encarbassot/keyboard/documentation/joystik.png

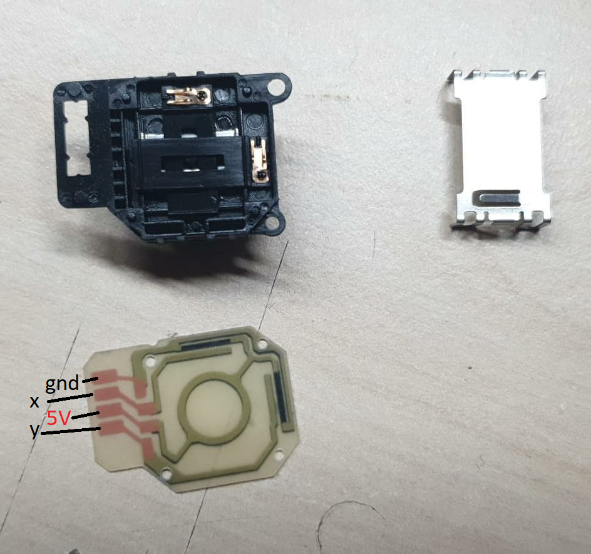
documentation/joystik.png
