encarbassot/keyboard/documentation/proMicro-deco-mux.png

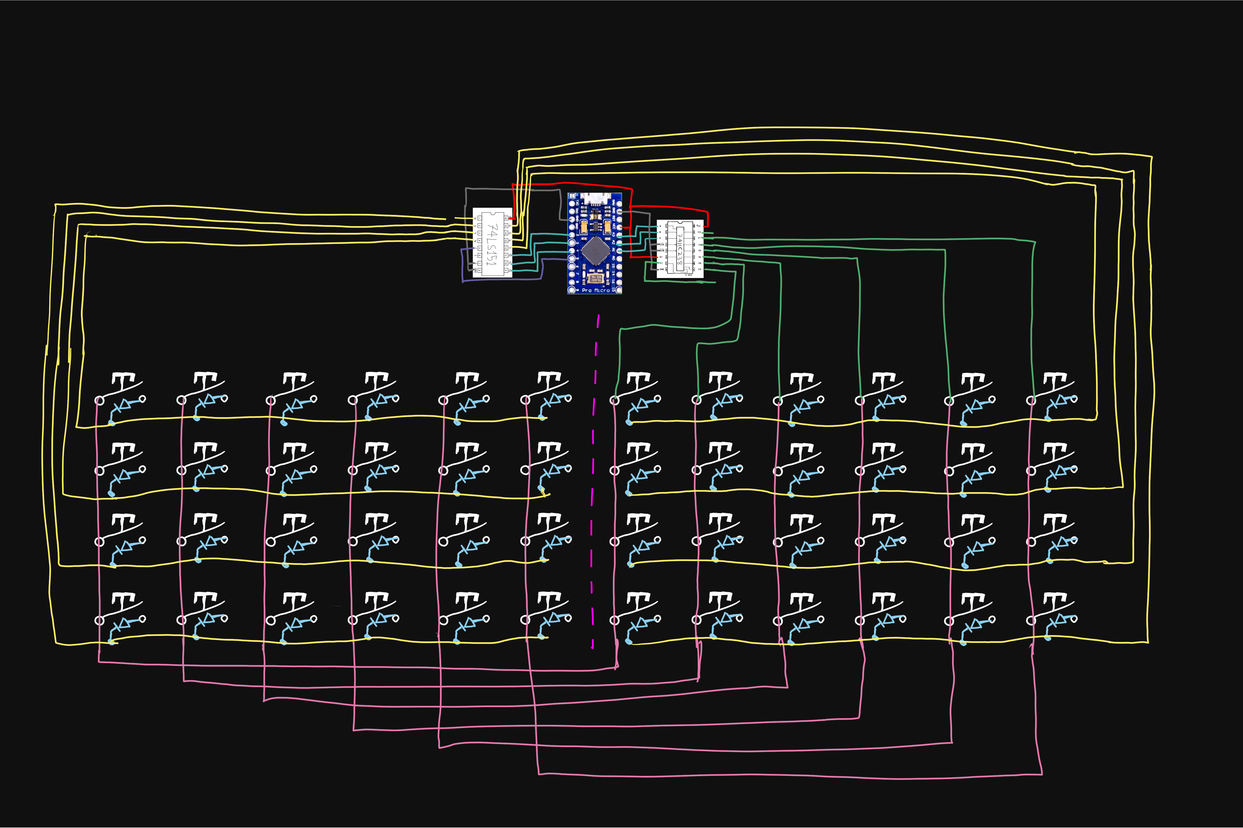
documentation/proMicro-deco-mux.png
