encarbassot/keyboard/img/media/circuit_1_deco_mux.jpg

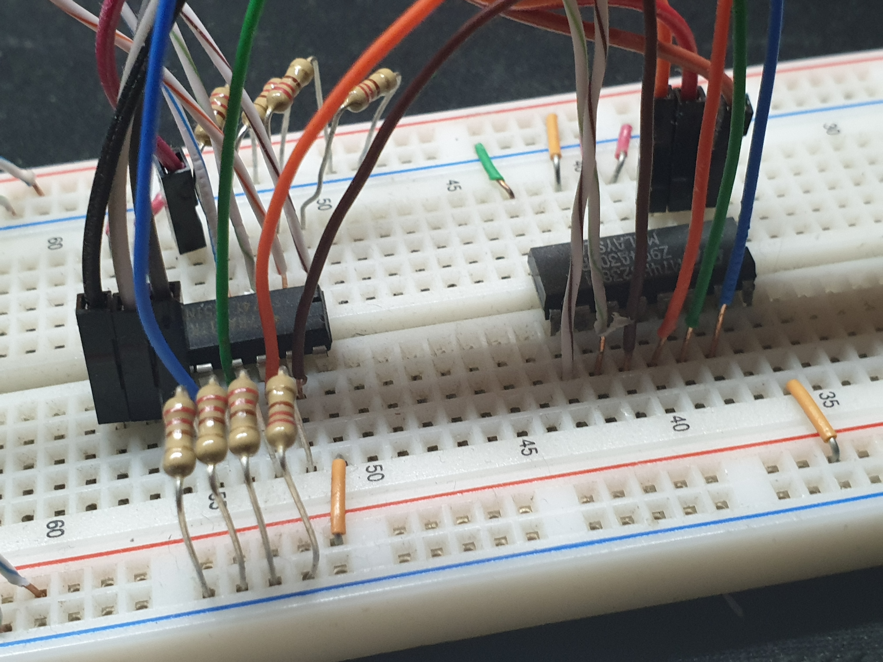
img/media/circuit_1_deco_mux.jpg
