encarbassot/keyboard/img/media/circuit_2_keyb48.jpg

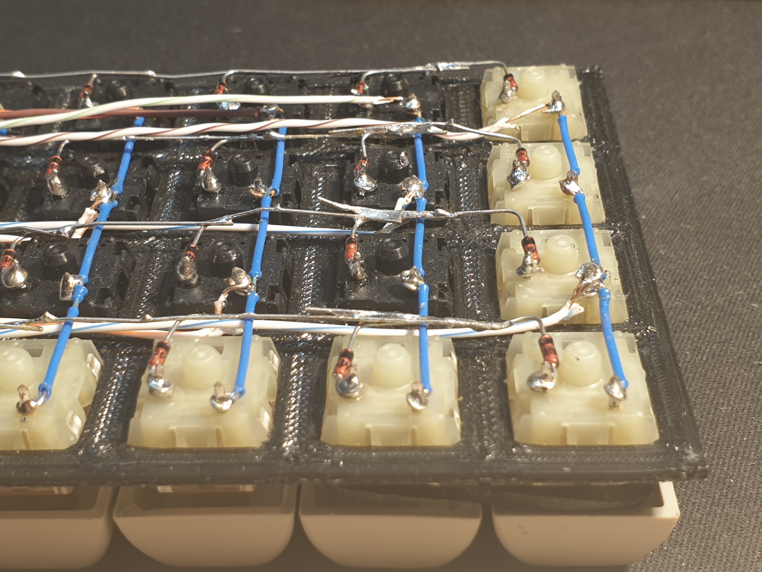
img/media/circuit_2_keyb48.jpg
