encarbassot/keyboard/img/media/circuit_3_deco_mux.jpeg

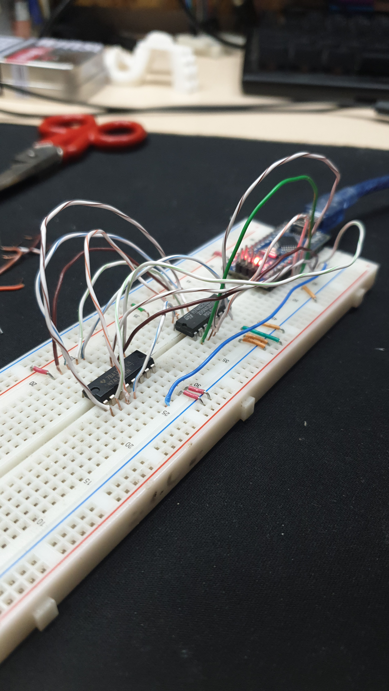
img/media/circuit_3_deco_mux.jpeg
