encarbassot/keyboard/img/media/keyb48_1.jpg

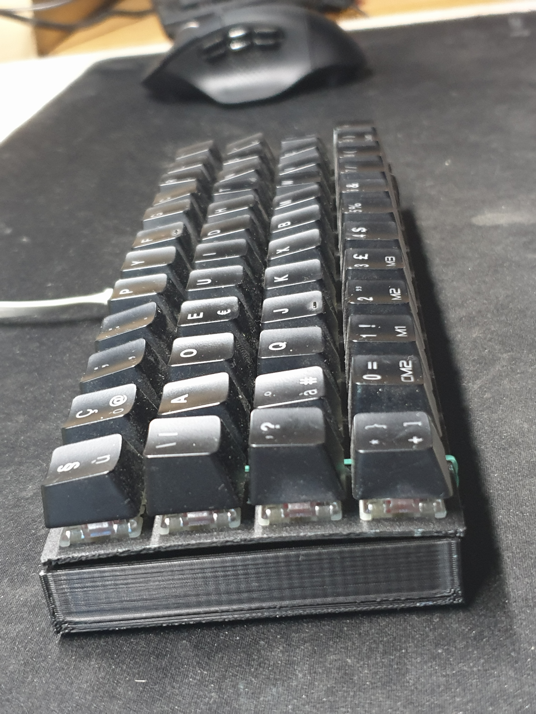
img/media/keyb48_1.jpg
