encarbassot/keyboard/img/media/keyb48_2.jpg

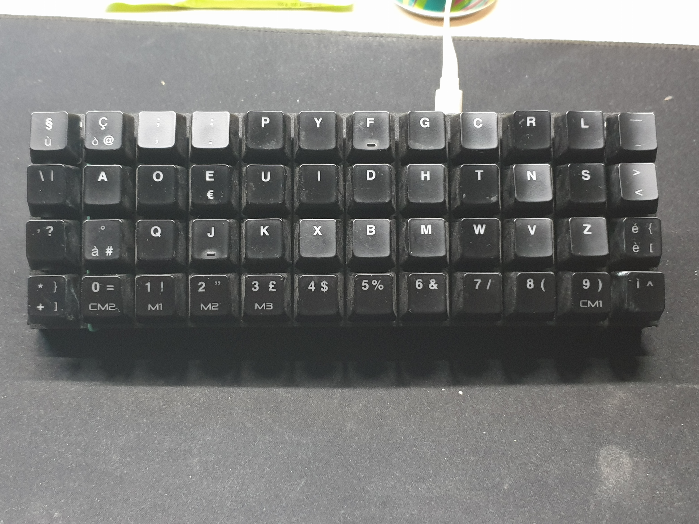
img/media/keyb48_2.jpg
