encarbassot/keyboard/img/media/keyb48_5.jpg

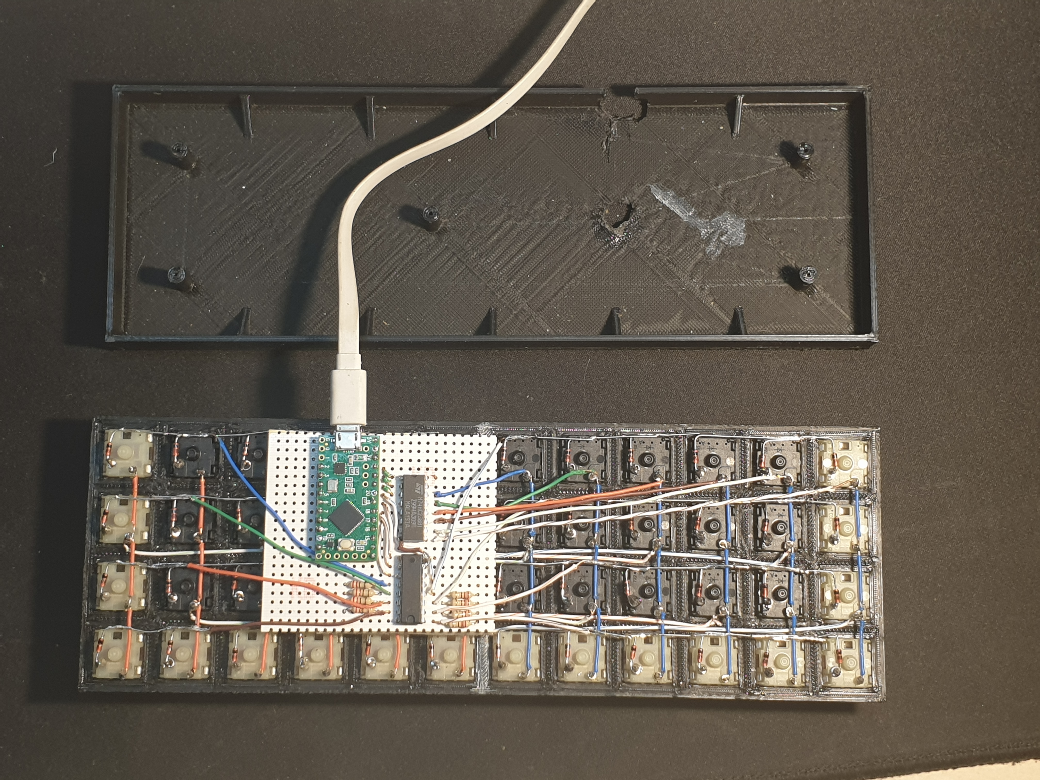
img/media/keyb48_5.jpg
