encarbassot/keyboard/img/media/keyb64_2_keyb48.jpeg

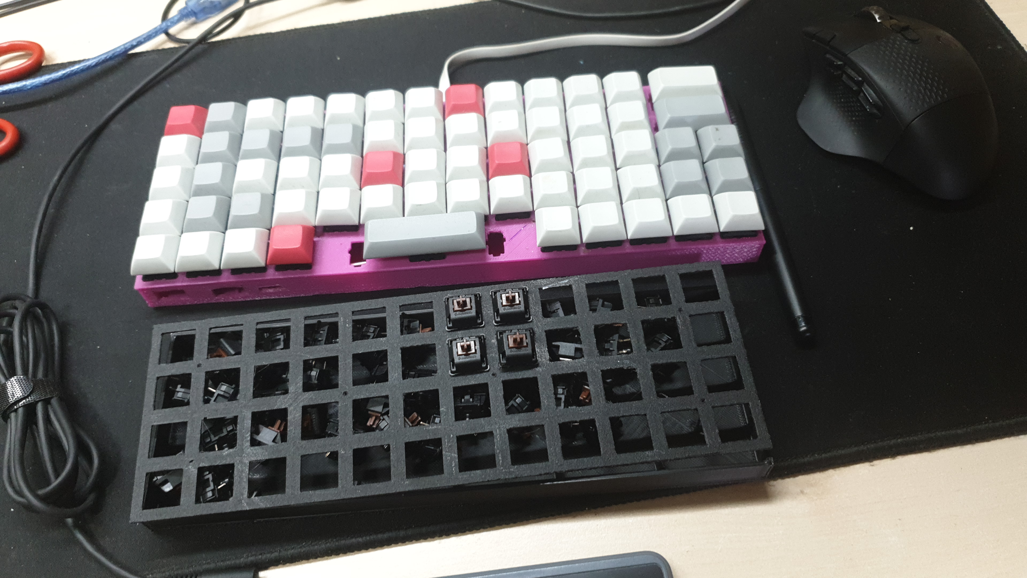
img/media/keyb64_2_keyb48.jpeg
