encarbassot/keyboard/img/media/numpad_2.jpg

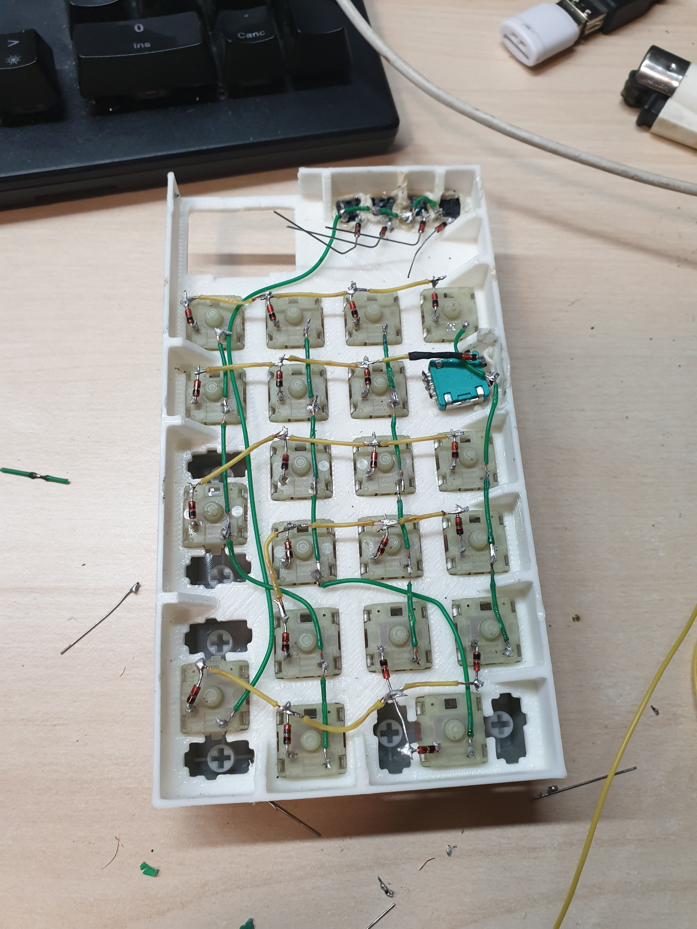
img/media/numpad_2.jpg
