encarbassot/keyboard/img/media/setup_1.jpg

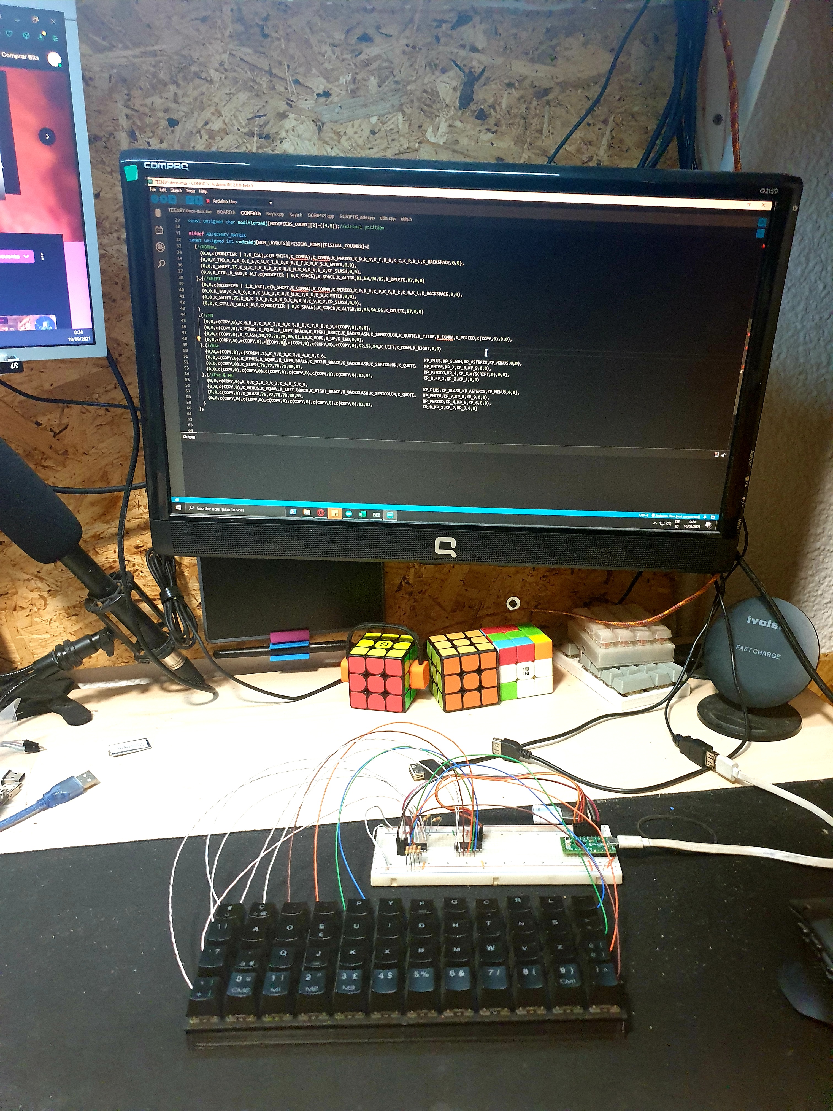
img/media/setup_1.jpg
