encarbassot/keyboard/img/media/setup_2.webp

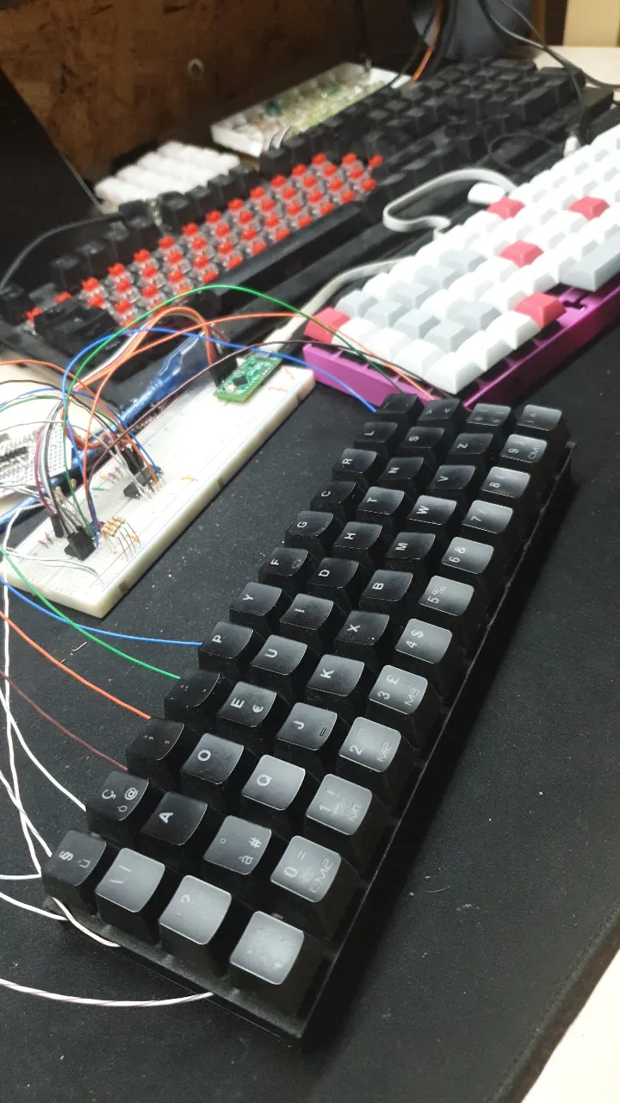
img/media/setup_2.webp
