encarbassot/keyboard/img/media/setup_3.jpeg

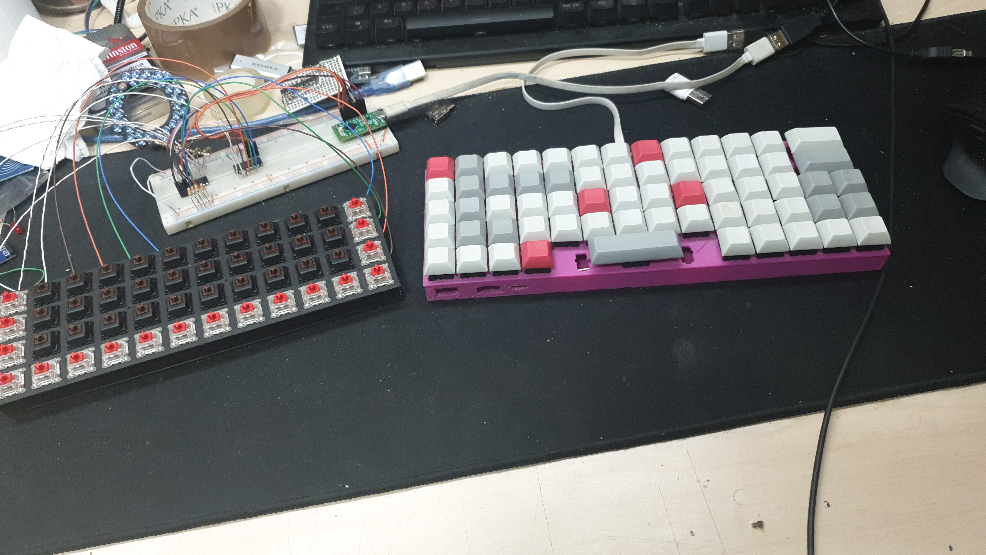
img/media/setup_3.jpeg
