encarbassot/keyboard/playground/ascii/ascii.ino

#include <Keyboard.h>

void setup() {
  //Initialize serial and wait for port to open:
  Keyboard.begin();
  delay(500);

  // prints title with ending line break
  Keyboard.println("ASCII Table ~ Character Map");
}

// first visible ASCIIcharacter '!' is number 33:
int thisByte = 32;
// you can also write ASCII characters in single quotes.
// for example, '!' is the same as 33, so you could also use this:
// int thisByte = '!';

void loop() {
  // prints value unaltered, i.e. the raw binary version of the byte.
  // The Serial Monitor interprets all bytes as ASCII, so 33, the first number,
  // will show up as '!'
  Keyboard.write(thisByte);

  Keyboard.print(" ");
  // prints value as string as an ASCII-encoded decimal (base 10).
  // Decimal is the default format for Serial.print() and Serial.println(),
  // so no modifier is needed:
  Keyboard.print(thisByte);
  // But you can declare the modifier for decimal if you want to.
  // this also works if you uncomment it:

  // Serial.print(thisByte, DEC);


  Keyboard.print(" 0x");
  // prints value as string in hexadecimal (base 16):
  Keyboard.print(thisByte, HEX);


  Keyboard.print(" 0b");
  // prints value as string in binary (base 2) also prints ending line break:
  Keyboard.println(thisByte, BIN);

  // if printed last visible character '~' or 126, stop:
  if (thisByte == 126) {    // you could also use if (thisByte == '~') {
    // This loop loops forever and does nothing
    while (true) {
      continue;
    }
  }
  // go on to the next character
  thisByte++;
}
/*
ASCII Table ª Character Map ESP
    32 0x20 0b100000
  ! 33 0x21 0b100001
  ¨ 34 0x22 0b100010
  · 35 0x23 0b100011
  $ 36 0x24 0b100100
  % 37 0x25 0b100101
  / 38 0x26 0b100110
  ´ 39 0x27 0b100111
  ) 40 0x28 0b101000
  = 41 0x29 0b101001
  ( 42 0x2A 0b101010
  ¿ 43 0x2B 0b101011
  , 44 0x2C 0b101100
  ' 45 0x2D 0b101101
  . 46 0x2E 0b101110
  - 47 0x2F 0b101111
  0 48 0x30 0b110000
  1 49 0x31 0b110001
  2 50 0x32 0b110010
  3 51 0x33 0b110011
  4 52 0x34 0b110100
  5 53 0x35 0b110101
  6 54 0x36 0b110110
  7 55 0x37 0b110111
  8 56 0x38 0b111000
  9 57 0x39 0b111001
  Ñ 58 0x3A 0b111010
  ñ 59 0x3B 0b111011
  ; 60 0x3C 0b111100
  ¡ 61 0x3D 0b111101
  : 62 0x3E 0b111110
  _ 63 0x3F 0b111111
  " 64 0x40 0b1000000
  A 65 0x41 0b1000001
  B 66 0x42 0b1000010
  C 67 0x43 0b1000011
  D 68 0x44 0b1000100
  E 69 0x45 0b1000101
  F 70 0x46 0b1000110
  G 71 0x47 0b1000111
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
 */

 /*
ASCII Table ~ Character Map ENG
    32 0x20 0b100000
  ! 33 0x21 0b100001
  " 34 0x22 0b100010
  # 35 0x23 0b100011
  $ 36 0x24 0b100100
  % 37 0x25 0b100101
  & 38 0x26 0b100110
  ' 39 0x27 0b100111
  ( 40 0x28 0b101000
  ) 41 0x29 0b101001
  * 42 0x2A 0b101010
  + 43 0x2B 0b101011
  , 44 0x2C 0b101100
  - 45 0x2D 0b101101
  . 46 0x2E 0b101110
  / 47 0x2F 0b101111
  0 48 0x30 0b110000
  1 49 0x31 0b110001
  2 50 0x32 0b110010
  3 51 0x33 0b110011
  4 52 0x34 0b110100
  5 53 0x35 0b110101
  6 54 0x36 0b110110
  7 55 0x37 0b110111
  8 56 0x38 0b111000
  9 57 0x39 0b111001
  : 58 0x3A 0b111010
  ; 59 0x3B 0b111011
  < 60 0x3C 0b111100
  = 61 0x3D 0b111101
  > 62 0x3E 0b111110
  ? 63 0x3F 0b111111
  @ 64 0x40 0b1000000
  A 65 0x41 0b1000001
  B 66 0x42 0b1000010
  C 67 0x43 0b1000011
  D 68 0x44 0b1000100
  E 69 0x45 0b1000101
  F 70 0x46 0b1000110
  G 71 0x47 0b1000111
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
  * 
  */
