encarbassot/keyboard/playground/bluetooth/bluetooth.ino

/*
  Software serial multple serial test

 Receives from the hardware serial, sends to software serial.
 Receives from software serial, sends to hardware serial.

 The circuit:
 * RX is digital pin 2 (connect to TX of other device)
 * TX is digital pin 3 (connect to RX of other device)

 Note:
 Not all pins on the Mega and Mega 2560 support change interrupts,
 so only the following can be used for RX:
 10, 11, 12, 13, 50, 51, 52, 53, 62, 63, 64, 65, 66, 67, 68, 69

 Not all pins on the Leonardo support change interrupts,
 so only the following can be used for RX:
 8, 9, 10, 11, 14 (MISO), 15 (SCK), 16 (MOSI).

 created back in the mists of time
 modified 25 May 2012
 by Tom Igoe
 based on Mikal Hart's example

 This example code is in the public domain.

 */
#include <SoftwareSerial.h>

SoftwareSerial bt(9,8); // RX, TX

void setup(){
  // Open serial communications and wait for port to open:
  Serial.begin(9600);
  while (!Serial) {
    ; // wait for serial port to connect. Needed for Native USB only
  }


  Serial.println("Goodnight moon!");

  // set the data rate for the SoftwareSerial port
  bt.begin(9600);
  delay(5000);
  bt.print("AT+PIN1465");
}

void loop(){

  if(bt.available()){    // Si llega un dato por el puerto BT se envía al monitor serial
  
    Serial.write(bt.read());
  }
 
  if(Serial.available()){  // Si llega un dato por el monitor serial se envía al puerto BT
  
     bt.write(Serial.read());
  }
  
}
